antoinecellerier/firebeetle-esp32-e-thermometer/docs/firebeetle2-esp32e-bmp390l-GDEH0154Z90-screen-refresh-Os.png

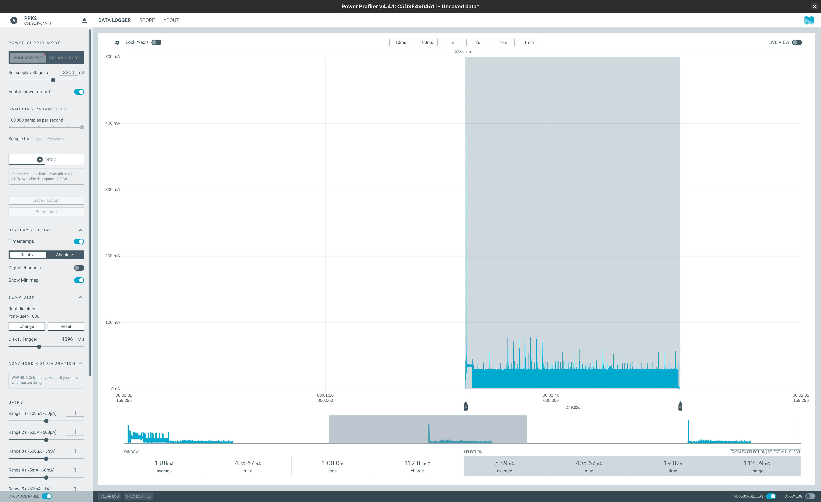
docs/firebeetle2-esp32e-bmp390l-GDEH0154Z90-screen-refresh-Os.png
