antoinecellerier/firebeetle-esp32-e-thermometer/docs/xiao-c6-bat-pads-3V2-bootloop-then-dead.png

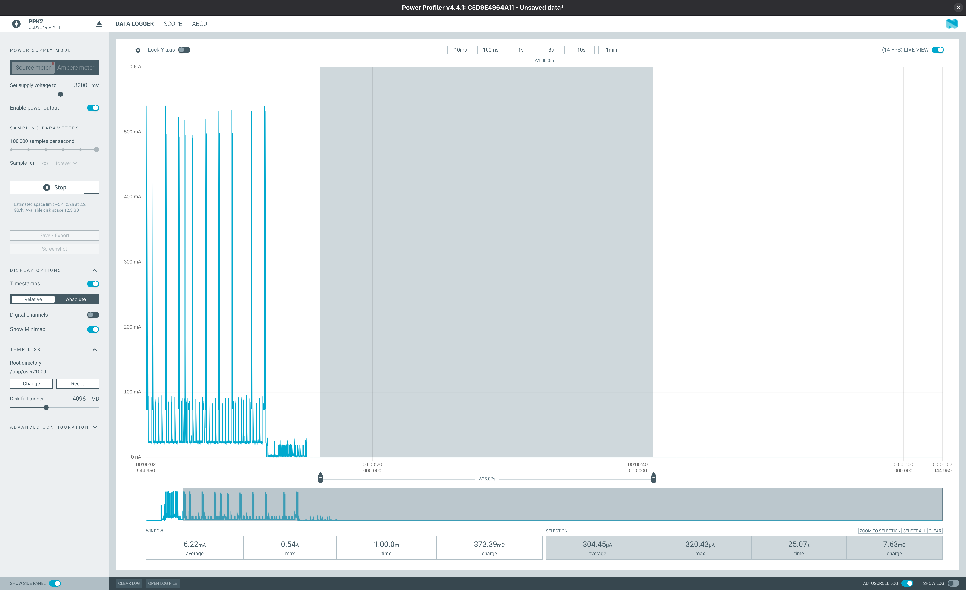
docs/xiao-c6-bat-pads-3V2-bootloop-then-dead.png
