antoinecellerier/firebeetle-esp32-e-thermometer/docs/xiao-c6-bat-pads-3V3-dropout-sawtooth-zoom.png

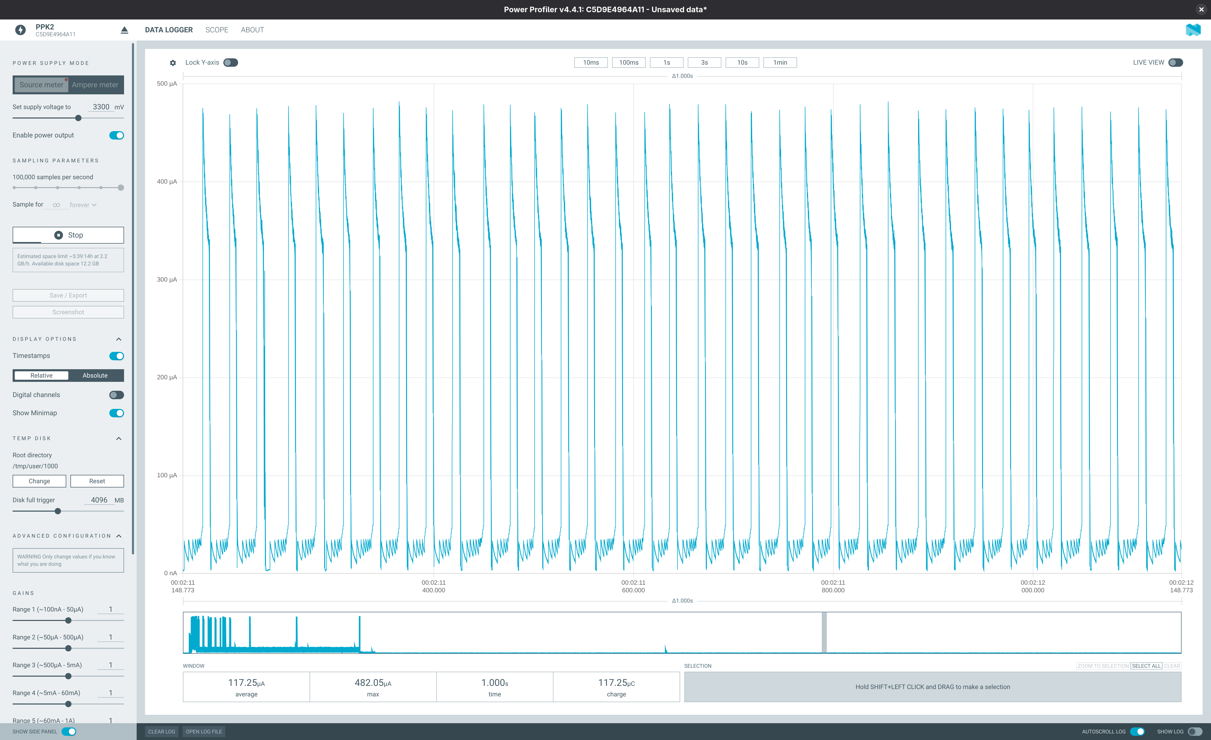
docs/xiao-c6-bat-pads-3V3-dropout-sawtooth-zoom.png
