antoinecellerier/firebeetle-esp32-e-thermometer/docs/xiao-c6-bat-pads-3V6-sag-with-storm.png

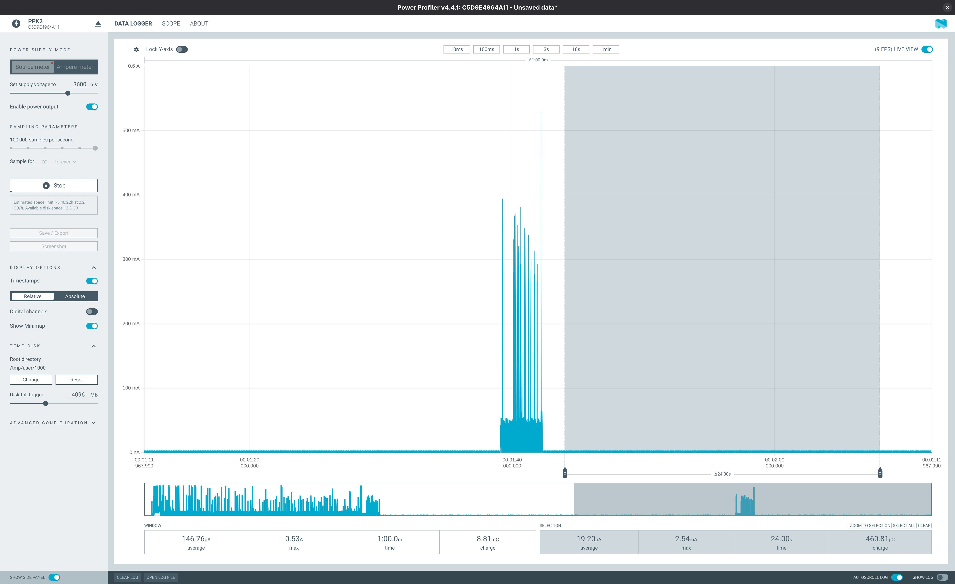
docs/xiao-c6-bat-pads-3V6-sag-with-storm.png
