antoinecellerier/firebeetle-esp32-e-thermometer/docs/xiao-c6-bat-pads-3V9-floor-after-boot.png

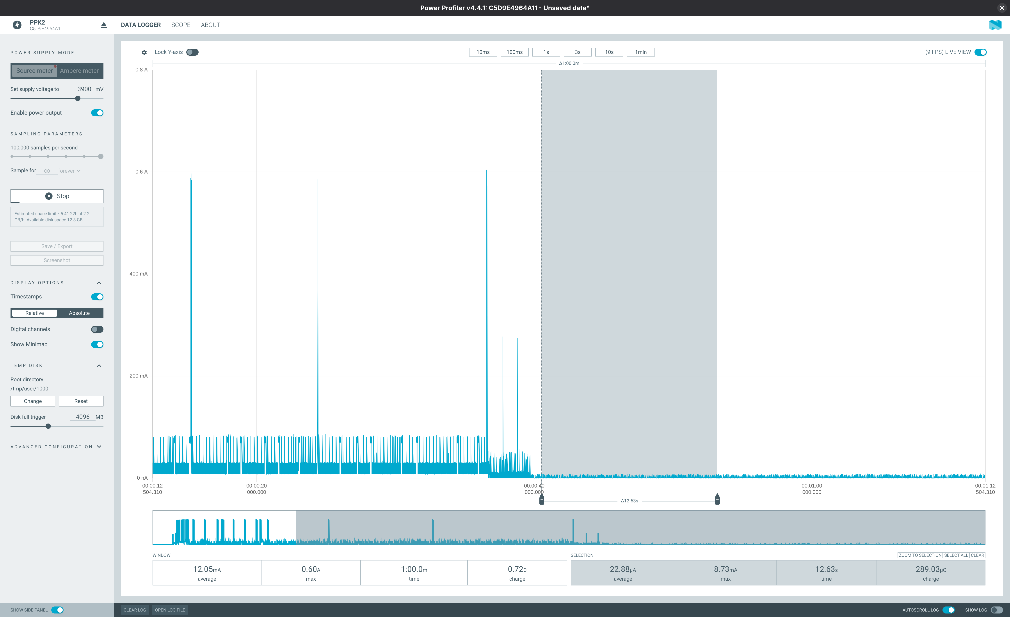
docs/xiao-c6-bat-pads-3V9-floor-after-boot.png
