antoinecellerier/firebeetle-esp32-e-thermometer/docs/xiao-c6-bat-pads-4V2-floor-zoom.png

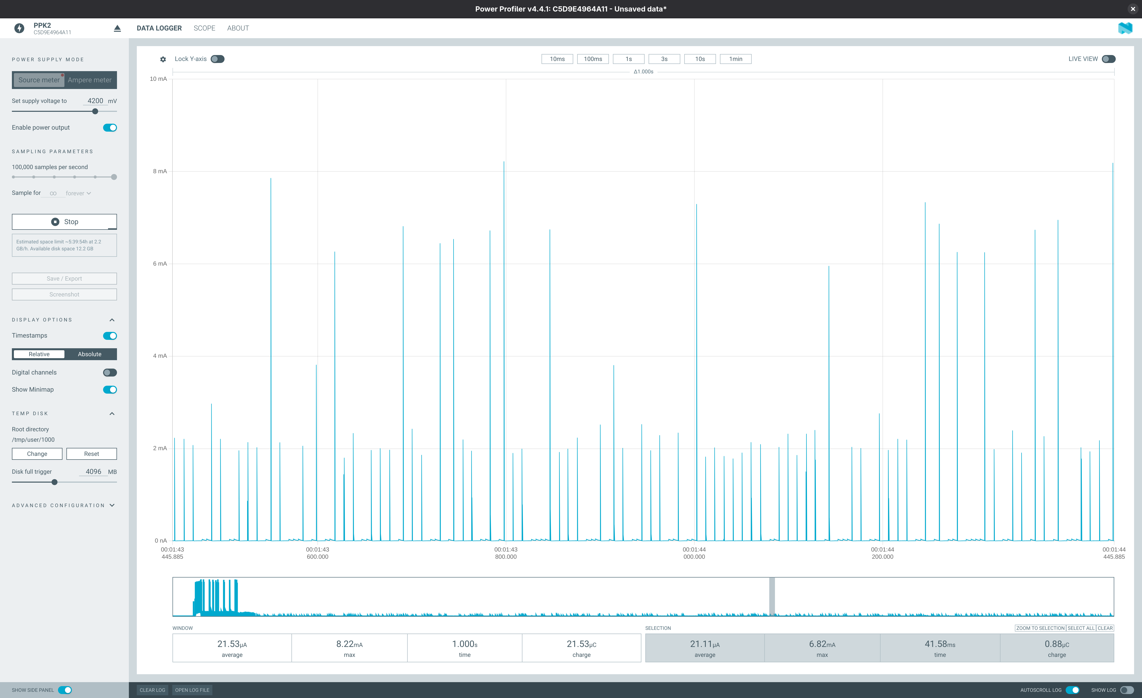
docs/xiao-c6-bat-pads-4V2-floor-zoom.png
