antoinecellerier/firebeetle-esp32-e-thermometer/docs/xiao-seeed-esp32c6-bmp581-deep-sleep-i2c-lp-core-read.png

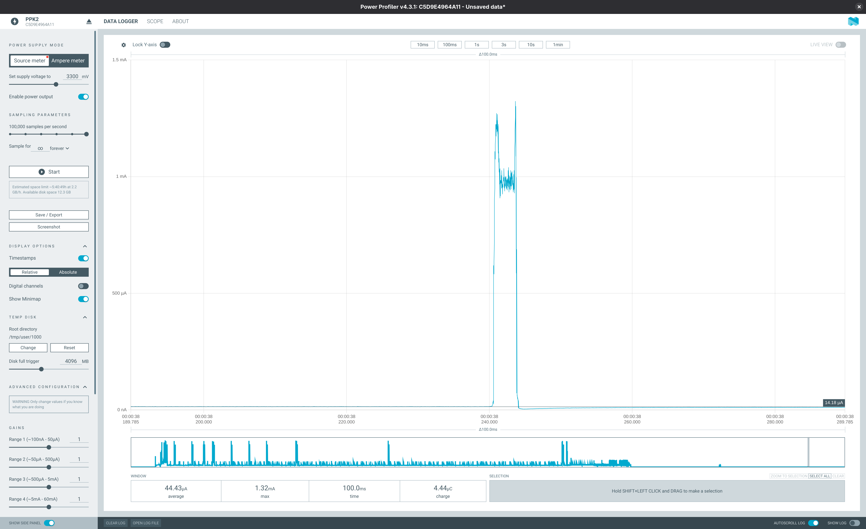
docs/xiao-seeed-esp32c6-bmp581-deep-sleep-i2c-lp-core-read.png
