antoinecellerier/firebeetle-esp32-e-thermometer/docs/xiao-seeed-esp32c6-bmp581-GDEH0576T81-screen-refresh.png

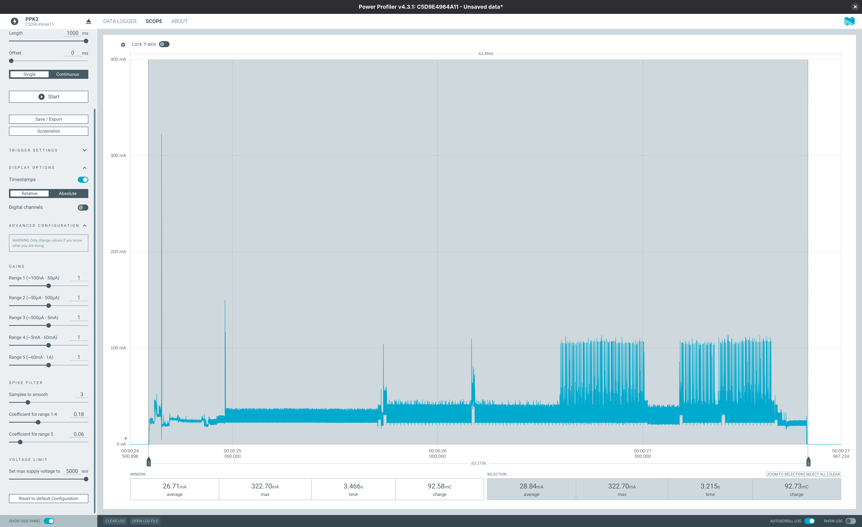
docs/xiao-seeed-esp32c6-bmp581-GDEH0576T81-screen-refresh.png
