antoinecellerier/firebeetle-esp32-e-thermometer/docs/xiao-seeed-esp32c6-seeed-epd-board-GDEW029I6FD-eta9740-battery-path-floor.png

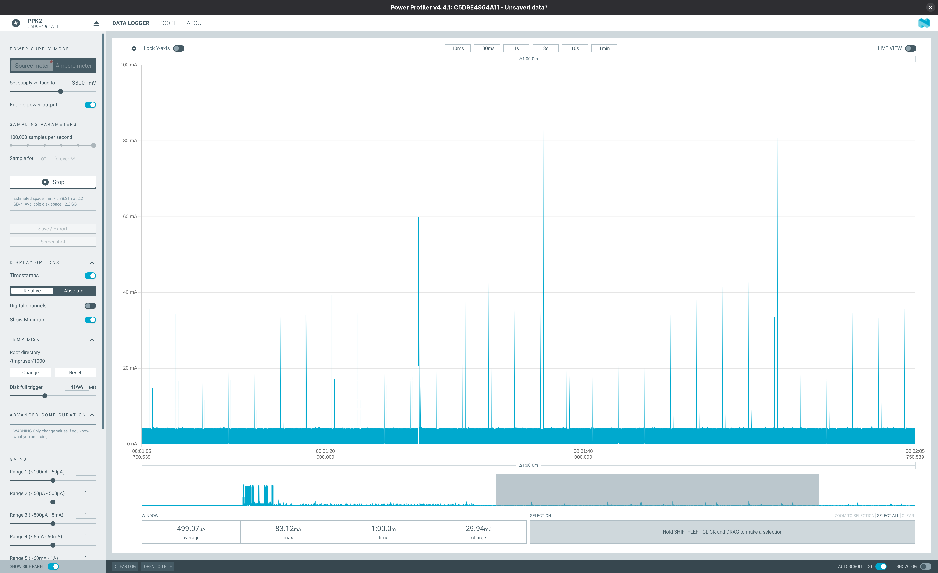
docs/xiao-seeed-esp32c6-seeed-epd-board-GDEW029I6FD-eta9740-battery-path-floor.png
