antoinecellerier/firebeetle-esp32-e-thermometer/docs/xiao-seeed-esp32c6-seeed-epd-board-GDEW029I6FD-screen-refresh.png

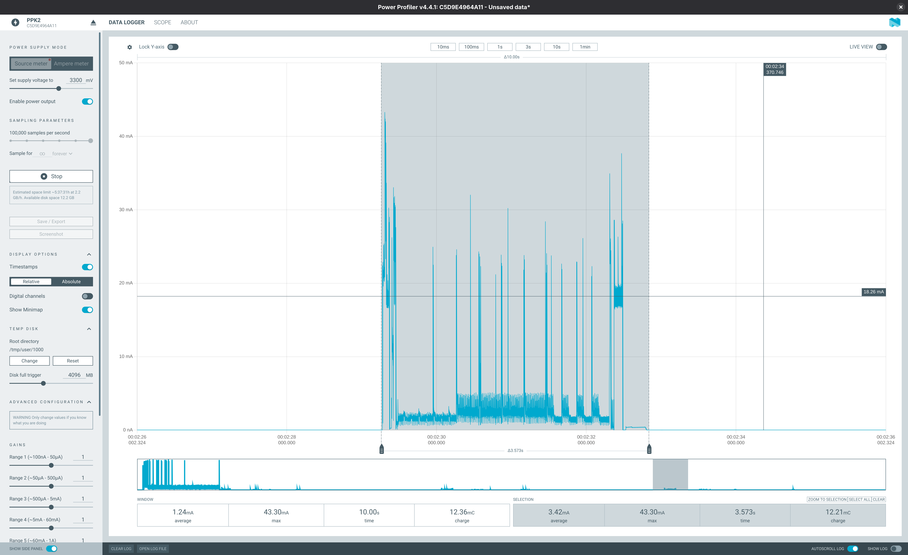
docs/xiao-seeed-esp32c6-seeed-epd-board-GDEW029I6FD-screen-refresh.png
