antoinecellerier/firebeetle-esp32-e-thermometer/docs/firebeetle2-esp32e-bmp390l-GDEH0154Z90-wake-active-phase-skip-validate.png

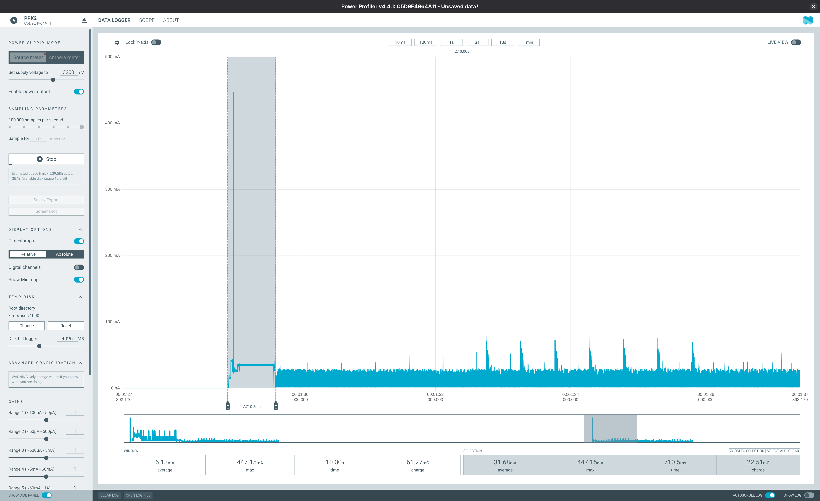
docs/firebeetle2-esp32e-bmp390l-GDEH0154Z90-wake-active-phase-skip-validate.png
