antoinecellerier/firebeetle-esp32-e-thermometer/docs/xiao-seeed-esp32c6-bmp581-GDEH0576T81-wake-active-phase-skip-validate-Os.png

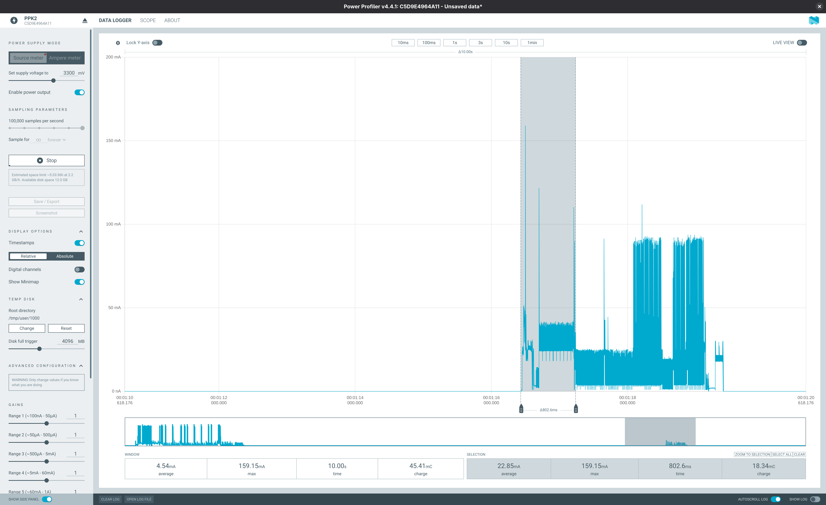
docs/xiao-seeed-esp32c6-bmp581-GDEH0576T81-wake-active-phase-skip-validate-Os.png
