antoinecellerier/firebeetle-esp32-e-thermometer/hardware/thermometer-c6/verify/drc_summary.py

#!/usr/bin/env python3
"""Compact text digest of out/drc.json (kicad-cli pcb drc --format json).

Usage: python3 verify/drc_summary.py [out/drc.json] [--top N] [--gate|--gate-fab]

Default: one summary line + up to N items per non-empty category (type,
description, mm coords). Exits 1 if any item exists, 0 if clean.

--gate: classify by type into REAL / DEFERRED / WAIVED and exit 0 iff REAL == 0.
This is the M5 copper-legality signal: WAIVED = M6 pours (starved_thermal) and
M7 silk; DEFERRED = dangling copper / unconnected nets that vanish once every
net routes and the GND pour lands; REAL = actual clearance/width/hole/short
violations -- the only ones that gate PathFinder's go/no-go. Reading this
instead of the raw drc.json (or DRC PNGs) keeps the routing loop cheap.

--gate-fab: the STRICT ship gate for `make fab`. Same classification, but a
finished board may not merely postpone anything, so it exits 0 iff REAL == 0
AND DEFERRED == 0 -- every remaining violation must be explicitly waived by a
scoped rule. It prints the WAIVED list with a reason per entry so the fab log
records exactly what shipped and why. (The J3 edge-launch copper_edge_clearance
waiver is GONE as of the 2026-07-20 datum respin: it waived a placement error,
not a design intent. WAIVED is expected to be empty.)
"""
import json
import os
import sys

HERE = os.path.dirname(os.path.abspath(__file__))
PROJECT = os.path.dirname(HERE)
DEFAULT = os.path.join(PROJECT, "out", "drc.json")

CATS = ("violations", "unconnected_items", "schematic_parity")

# M6 (GND pours) and M7 (silk) are later milestones -- never a copper gate.
WAIVED = {"starved_thermal", "silk_edge_clearance", "silk_overlap",
          "silk_over_copper"}
# Expected while nets are still unrouted / the GND pour is absent; they clear
# once M5 hits zero stragglers and M6 lands. Reported, but don't fail the gate.
DEFERRED = {"track_dangling", "via_dangling", "unconnected_items"}
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
